dhansel/IECBuddy/software/IECBuddy/src/VDrive/fsimage-gcr.c

/*
 * fsimage-gcr.c
 *
 * Written by
 *  Andreas Boose <viceteam@t-online.de>
 *
 * This file is part of VICE, the Versatile Commodore Emulator.
 * See README for copyright notice.
 *
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
 */

#include <stdio.h>
#include <string.h>

#include "diskconstants.h"
#include "diskimage.h"
#include "fsimage-gcr.h"
#include "fsimage.h"
#include "gcr.h"
#include "cbmdos.h"
#include "log.h"
#include "lib.h"
#include "types.h"
#include "util.h"


static log_t fsimage_gcr_log = LOG_DEFAULT;
static const uint8_t gcr_image_header_expected_1541[] =
    { 0x47, 0x43, 0x52, 0x2D, 0x31, 0x35, 0x34, 0x31, 0x00 };
static const uint8_t gcr_image_header_expected_1571[] =
    { 0x47, 0x43, 0x52, 0x2D, 0x31, 0x35, 0x37, 0x31, 0x00 };

/*-----------------------------------------------------------------------*/
/* Intial GCR buffer setup.  */

int fsimage_read_gcr_image(const disk_image_t *image)
{
    unsigned int half_track;

    for (half_track = 0; half_track < MAX_GCR_TRACKS; half_track++) {
        /* free existing track */
        if (image->gcr->tracks[half_track].data) {
            lib_free(image->gcr->tracks[half_track].data);
            image->gcr->tracks[half_track].data = NULL;
            image->gcr->tracks[half_track].size = 0;
        }
        /* load new track from image */
        if (half_track < image->max_half_tracks) {
            fsimage_gcr_read_half_track(image, half_track + 2, &image->gcr->tracks[half_track]);
        } else {
            /* create empty tracks for non existing tracks */
            image->gcr->tracks[half_track].size = disk_image_raw_track_size(image->type, half_track / 2);
            image->gcr->tracks[half_track].data = lib_malloc(image->gcr->tracks[half_track].size);
            memset(image->gcr->tracks[half_track].data, 0, image->gcr->tracks[half_track].size);
        }
    }

    return 0;
}
/*-----------------------------------------------------------------------*/
/* Seek to half track */

static long fsimage_gcr_seek_half_track(fsimage_t *fsimage, unsigned int half_track,
                                        uint16_t *max_track_length, uint8_t *num_half_tracks)
{
    uint8_t buf[12];

    if ( !archdep_fisopen(fsimage->fd) ) {
        log_error(fsimage_gcr_log, "Attempt to read without disk image.");
        return -1;
    }
    if (util_fpread(fsimage->fd, buf, 12, 0) < 0) {
        log_error(fsimage_gcr_log, "Could not read GCR disk image.");
        return -1;
    }
    if ((memcmp(gcr_image_header_expected_1541, buf, sizeof(gcr_image_header_expected_1541)) != 0)
        && (memcmp(gcr_image_header_expected_1571, buf, sizeof(gcr_image_header_expected_1571)) != 0)) {
        log_error(fsimage_gcr_log, "Unexpected GCR header found." );
        return -1;
    }

    *num_half_tracks = buf[9];
    if (*num_half_tracks > MAX_GCR_TRACKS) {
        log_error(fsimage_gcr_log, "Too many half tracks." );
        return -1;
    }

    *max_track_length = util_le_buf_to_word(&buf[10]);
#if 0
    /* if 0'ed because:
       *max_track_length is of type WORD and NUM_MAX_MEM_BYTES_TRACK is 65536
     */
    if (*max_track_length > NUM_MAX_MEM_BYTES_TRACK) {
        log_error(fsimage_gcr_log, "Too large max track length.");
        return -1;
    }
#endif

    if (util_fpread(fsimage->fd, buf, 4, 12 + (half_track - 2) * 4) < 0) {
        log_error(fsimage_gcr_log, "Could not read GCR disk image.");
        return -1;
    }
    return util_le_buf_to_dword(buf);
}

/*-----------------------------------------------------------------------*/
/* Read an entire GCR track from the disk image.  */

int fsimage_gcr_read_half_track(const disk_image_t *image, unsigned int half_track,
                                disk_track_t *raw)
{
    uint16_t track_len;
    uint8_t buf[4];
    long offset;
    fsimage_t *fsimage;
    uint16_t max_track_length;
    uint8_t num_half_tracks;
    unsigned int orig_half_track = half_track;

    fsimage = image->media.fsimage;

    raw->data = NULL;
    raw->size = 0;

    while( raw->data==NULL )
      {
        offset = fsimage_gcr_seek_half_track(fsimage, half_track, &max_track_length, &num_half_tracks);

        if (offset < 0) {
          return -1;
        }

        if (offset != 0) {
          if (util_fpread(fsimage->fd, buf, 2, offset) < 0) {
            log_error(fsimage_gcr_log, "Could not read GCR disk image.");
            return -1;
          }

          track_len = util_le_buf_to_word(buf);

          if ((track_len < 1) || (track_len > max_track_length)) {
            log_error(fsimage_gcr_log,
                      "Track field length %u is not supported.",
                      track_len);
            return -1;
          }

          raw->data = lib_calloc(1, track_len);
          raw->size = track_len;

          if (archdep_fread(raw->data, track_len, 1, fsimage->fd) < 1) {
            log_error(fsimage_gcr_log, "Could not read GCR disk image.");
            return -1;
          }
        } else {
          raw->size = disk_image_raw_track_size(image->type, half_track / 2);
          raw->data = lib_malloc(raw->size);
          memset(raw->data, 0x55, raw->size);
        }

        /* the following can be #if 0'd to skip looking for actual track number */
#if 1
        static int current_half_track = -1;
        if( half_track != current_half_track )
          {
            uint8_t track;

            /* read track number in first header found on this track */
            fdc_err_t rf = gcr_read_track_number(raw, &track);
            
            /* if a header was found and track number is different from expected
               then set next_half_track to where we expect the actual track */
            unsigned int next_half_track;
            if( rf==CBMDOS_FDC_ERR_OK )
              next_half_track = half_track + ((int) half_track - (int) 2*track);
            else
              next_half_track = half_track;
            
            /* if next_half_track does not match half_track then repeat the loop
               to read next_half_track */
            if( next_half_track!=half_track && next_half_track!=orig_half_track )
              {
                log_error(fsimage_gcr_log,
                          "Track number mismatch: expected %u, found %u, now reading track %u.",
                          half_track/2, track, next_half_track/2);
                
                half_track = next_half_track;
                lib_free(raw->data);
                raw->data = NULL;
                raw->size = 0;
              }
            else
              current_half_track = half_track;
          }
#endif
      }
    
    return 0;
}

static int fsimage_gcr_read_track(const disk_image_t *image, unsigned int track,
                                  disk_track_t *raw)
{
    return fsimage_gcr_read_half_track(image, track << 1, raw);
}

/*-----------------------------------------------------------------------*/
/* Write an entire GCR track to the disk image.  */

int fsimage_gcr_write_half_track(disk_image_t *image, unsigned int half_track,
                                 const disk_track_t *raw)
{
    int gap;
    int extend = 0;
    long res;
    uint16_t max_track_length;
    uint8_t buf[4];
    long offset;
    fsimage_t *fsimage;
    uint8_t num_half_tracks;

    fsimage = image->media.fsimage;

    offset = fsimage_gcr_seek_half_track(fsimage, half_track, &max_track_length, &num_half_tracks);
    if (offset < 0) {
        return -1;
    }
    if (image->read_only != 0) {
        log_error(fsimage_gcr_log,
                  "Attempt to write to read-only disk image.");
        return -1;
    }

    if (raw->size > max_track_length) {
        log_error(fsimage_gcr_log,
                  "Track too long for image.");
        return -1;
    }

    if (offset == 0) {
        offset = archdep_fseek(fsimage->fd, 0, SEEK_END);
        if (offset == 0) {
            offset = archdep_ftell(fsimage->fd);
        }
        if (offset < 0) {
            log_error(fsimage_gcr_log, "Could not extend GCR disk image.");
            return -1;
        }
        extend = 1;
    }

    if (raw->data != NULL) {
        util_word_to_le_buf(buf, (uint16_t)raw->size);

        if (util_fpwrite(fsimage->fd, buf, 2, offset) < 0) {
            log_error(fsimage_gcr_log, "Could not write GCR disk image.");
            return -1;
        }

        /* Clear gap between the end of the actual track and the start of
           the next track.  */
        if (archdep_fwrite(raw->data, raw->size, 1, fsimage->fd) < 1) {
            log_error(fsimage_gcr_log, "Could not write GCR disk image.");
            return -1;
        }
        gap = max_track_length - raw->size;

        if (gap > 0) {
            uint8_t *padding = lib_calloc(1, gap);
            res = archdep_fwrite(padding, gap, 1, fsimage->fd);
            lib_free(padding);
            if (res < 1) {
                log_error(fsimage_gcr_log, "Could not write GCR disk image.");
                return -1;
            }
        }

        if (extend) {
            /* FIXME: danger zone: 'DWORD' is a loose term, doesn't indicate
             *        a size, just that's the next bigger size of 'WORD'.
             *        Probably these terms are taken from the horrible Win API.
             *        -- compyx 2020-07-24
             */
            util_dword_to_le_buf(buf, (uint32_t)offset);
            if (util_fpwrite(fsimage->fd, buf, 4, 12 + (half_track - 2) * 4) < 0) {
                log_error(fsimage_gcr_log, "Could not write GCR disk image.");
                return -1;
            }

            util_dword_to_le_buf(buf, disk_image_speed_map(image->type, half_track / 2));
            if (util_fpwrite(fsimage->fd, buf, 4, 12 + (half_track - 2 + num_half_tracks) * 4) < 0) {
                log_error(fsimage_gcr_log, "Could not write GCR disk image.");
                return -1;
            }
        }
    }

    /* Make sure the stream is visible to other readers.  */
    archdep_fflush(fsimage->fd);

    return 0;
}

static int fsimage_gcr_write_track(disk_image_t *image, unsigned int track,
                                   const disk_track_t *raw)
{
    return fsimage_gcr_write_half_track(image, track << 1, raw);
}


/*-----------------------------------------------------------------------*/
/* Read a sector from the GCR disk image.  */

int fsimage_gcr_read_sector(const disk_image_t *image, uint8_t *buf, const disk_addr_t *dadr)
{
    fdc_err_t rf;

    if (dadr->track > image->tracks) {
        log_error(fsimage_gcr_log,
                  "Track %u out of bounds.  Cannot read GCR track.",
                  dadr->track);
        return -1;
    }

    if (image->gcr == NULL) {
        disk_track_t raw;
        if (fsimage_gcr_read_track(image, dadr->track, &raw) < 0) {
            return -1;
        }
        if (raw.data == NULL) {
            return CBMDOS_IPE_NOT_READY;
        }
        rf = gcr_read_sector(&raw, buf, (uint8_t)dadr->sector, image->id);
        lib_free(raw.data);
    } else {
       rf = gcr_read_sector(&image->gcr->tracks[(dadr->track * 2) - 2], buf, (uint8_t)dadr->sector, image->id);
    }
    if (rf != CBMDOS_FDC_ERR_OK) {
        log_error(fsimage_gcr_log,
                  "Cannot find track: %u sector: %u within GCR image.",
                  dadr->track, dadr->sector);
        return cbmdos_fdc_error_to_cbmdos_error(rf);
    }
    return CBMDOS_IPE_OK;
}


/*-----------------------------------------------------------------------*/
/* Write a sector to the GCR disk image.  */

int fsimage_gcr_write_sector(disk_image_t *image, const uint8_t *buf,
                             const disk_addr_t *dadr)
{
    if (dadr->track > image->tracks) {
        log_error(fsimage_gcr_log,
                  "Track %u out of bounds.  Cannot write GCR sector",
                  dadr->track);
        return -1;
    }

    if (image->gcr == NULL) {
        disk_track_t raw;
        if (fsimage_gcr_read_track(image, dadr->track, &raw) < 0
            || raw.data == NULL) {
            return -1;
        }
        if (gcr_write_sector(&raw, buf, (uint8_t)dadr->sector, image->id) != CBMDOS_FDC_ERR_OK) {
            log_error(fsimage_gcr_log,
                      "Could not find track %u sector %u in disk image",
                      dadr->track, dadr->sector);
            lib_free(raw.data);
            return -1;
        }
        if (fsimage_gcr_write_track(image, dadr->track, &raw) < 0) {
            lib_free(raw.data);
            return -1;
        }
        lib_free(raw.data);
    } else {
        if (gcr_write_sector(&image->gcr->tracks[(dadr->track * 2) - 2], buf, (uint8_t)dadr->sector, image->id) != CBMDOS_FDC_ERR_OK) {
            log_error(fsimage_gcr_log,
                      "Could not find track %u sector %u in disk image",
                      dadr->track, dadr->sector);
            return -1;
        }
        if (fsimage_gcr_write_track(image, dadr->track, &image->gcr->tracks[(dadr->track * 2) - 2]) < 0) {
            log_error(fsimage_gcr_log,
                      "Failed writing track %u to disk image.", dadr->track);
            return -1;
        }
    }

    return 0;
}

/*-----------------------------------------------------------------------*/

void fsimage_gcr_init(void)
{
    fsimage_gcr_log = log_open("Filesystem Image GCR");
}


int fsimage_gcr_read_disk_id(const struct disk_image_s *image, uint8_t track, uint8_t sector, uint16_t *id)
{
  fdc_err_t rf;

  if (image->gcr == NULL) 
    {
      disk_track_t raw;
      if( fsimage_gcr_read_track(image, track, &raw) < 0 )
        return CBMDOS_IPE_NOT_READY;

      if (raw.data == NULL)
        return CBMDOS_IPE_NOT_READY;
      
      rf = gcr_read_sector_id(&raw, id, sector);
      lib_free(raw.data);
    }
  else 
    rf = gcr_read_sector_id(&image->gcr->tracks[(track * 2) - 2], id, sector);

  return cbmdos_fdc_error_to_cbmdos_error(rf);
}
